Cuprum77/OpenTag/software/STM32WB_BT_TAG/STM32_WPAN/App/app_ble.c

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

/* Includes ------------------------------------------------------------------*/
#include "main.h"

#include "app_common.h"

#include "dbg_trace.h"
#include "ble.h"
#include "tl.h"
#include "app_ble.h"

#include "stm32_seq.h"
#include "shci.h"
#include "stm32_lpm.h"
#include "otp.h"

#include "custom_app.h"

/* USER CODE BEGIN Includes */
#include "stm32_lpm.h"
/* USER CODE END Includes */


/**
 * security parameters structure
 */
typedef struct _tSecurityParams
{
  /**
   * IO capability of the device
   */
  uint8_t ioCapability;

  /**
   * Authentication requirement of the device
   * Man In the Middle protection required?
   */
  uint8_t mitm_mode;

  /**
   * bonding mode of the device
   */
  uint8_t bonding_mode;

  /**
   * this variable indicates whether to use a fixed pin
   * during the pairing process or a passkey has to be
   * requested to the application during the pairing process
   * 0 implies use fixed pin and 1 implies request for passkey
   */
  uint8_t Use_Fixed_Pin;

  /**
   * minimum encryption key size requirement
   */
  uint8_t encryptionKeySizeMin;

  /**
   * maximum encryption key size requirement
   */
  uint8_t encryptionKeySizeMax;

  /**
   * fixed pin to be used in the pairing process if
   * Use_Fixed_Pin is set to 1
   */
  uint32_t Fixed_Pin;

  /**
   * this flag indicates whether the host has to initiate
   * the security, wait for pairing or does not have any security
   * requirements.
   * 0x00 : no security required
   * 0x01 : host should initiate security by sending the slave security
   *        request command
   * 0x02 : host need not send the clave security request but it
   * has to wait for paiirng to complete before doing any other
   * processing
   */
  uint8_t initiateSecurity;
  /* USER CODE BEGIN tSecurityParams*/

  /* USER CODE END tSecurityParams */
}tSecurityParams;

/**
 * global context
 * contains the variables common to all
 * services
 */
typedef struct _tBLEProfileGlobalContext
{
  /**
   * security requirements of the host
   */
  tSecurityParams bleSecurityParam;

  /**
   * gap service handle
   */
  uint16_t gapServiceHandle;

  /**
   * device name characteristic handle
   */
  uint16_t devNameCharHandle;

  /**
   * appearance characteristic handle
   */
  uint16_t appearanceCharHandle;

  /**
   * connection handle of the current active connection
   * When not in connection, the handle is set to 0xFFFF
   */
  uint16_t connectionHandle;

  /**
   * length of the UUID list to be used while advertising
   */
  uint8_t advtServUUIDlen;

  /**
   * the UUID list to be used while advertising
   */
  uint8_t advtServUUID[100];
  /* USER CODE BEGIN BleGlobalContext_t*/

  /* USER CODE END BleGlobalContext_t */
}BleGlobalContext_t;

typedef struct
{
  BleGlobalContext_t BleApplicationContext_legacy;
  APP_BLE_ConnStatus_t Device_Connection_Status;
  /* USER CODE BEGIN PTD_1*/

  /* USER CODE END PTD_1 */
}BleApplicationContext_t;

#define FAST_ADV_TIMEOUT               (30*1000*1000/CFG_TS_TICK_VAL) /**< 30s */
#define INITIAL_ADV_TIMEOUT            (60*1000*1000/CFG_TS_TICK_VAL) /**< 60s */

#define BD_ADDR_SIZE_LOCAL    6

/* USER CODE BEGIN PD */
/* Defines how long the tag will stay on and not go to sleep after a cold startup
 * This is useful to connect to a debugger or to check if the advertised payload is correct.
 */
#define COLD_START_ACTIVE_TIME_S 30

/*
* Turn on the LED when sending out advertising data, this is useful for debugging to see when the tag is advertising
* but should be disabled for normal use to save power. 
* (comment out to disable)
*/
#define ENABLE_ADV_LED_DEBUG

/* Defines the address where the airtag keys are put, this can be done with stm32cubeprogrammer, in the erasing and programming section,
 * you put in this address, select the option to NOT skip flash erase and program. The linker in this cubemx project is setup to not overwrite a 64k region after this address.
 */
#define KEY_ADDR_GOOGLE 0x08020000
#define KEY_ADDR_APPLE 0x08030000

#define GOOGLE_EID_LEN_BYTES 20
#define APPLE_KEY_LEN_BYTES 28

#define GOOGLE_NUMKEYS_FIELD_BYTES 2
#define APPLE_NUMKEYS_FIELD_BYTES 1

typedef enum adv_type {
  APPLE = 0,
  GOOGLE = 1
} adv_type_t;

// You can define the order and frequency of advertising here.
// Examples:
// adv_type_t adv_order[] = {APPLE, GOOGLE};          // alternate each cycle
// adv_type_t adv_order[] = {APPLE, APPLE, GOOGLE};   // advertise Apple twice as much as Google
// adv_type_t adv_order[] = {APPLE};                  // only advertise Apple
// adv_type_t adv_order[] = {GOOGLE};                 // only advertise Google
// Note that switching between the advertisement types takes a bit more time and thus energy
// So, it is better to repeat a key a few times before switching
adv_type_t adv_order[] = {APPLE, APPLE, APPLE, GOOGLE, GOOGLE, GOOGLE};

#define ADV_ORDER_LEN (sizeof(adv_order) / sizeof(adv_order[0]))

// Counted on startup and then used later to gate logic (so we can skip the paths that are never advertising)
int num_google = -1;
int num_apple = -1;
size_t adv_order_index = 0;

/* Define how often (long) a key will be reused after switching to the next one
 * The interval for one key is (DELAY_IN_S * REUSE_CYCLES => 10s * 360 cycles = changes key every 60 min)
 * Smaller number of cycles = key changes more often, but more keys needed.
 * You can calculate how much time it will take for all keys to be used up and it will roll around:
 * (DELAY_IN_S * REUSE_CYCLES * NUM_KEYS => 10s * 360 cycles * 32 keys = keys will wrap around every 32 hours)
 */
#define REUSE_CYCLES 360

/* A sleep cycle is 10 seconds of sleep, so 2 cycles is 20 seconds of sleep and so on.*/
#define SLEEP_CYCLES 1
/* USER CODE END PD */

PLACE_IN_SECTION("MB_MEM1") ALIGN(4) static TL_CmdPacket_t BleCmdBuffer;

static const uint8_t a_MBdAddr[BD_ADDR_SIZE_LOCAL] =
{
  (uint8_t)((CFG_ADV_BD_ADDRESS & 0x0000000000FF)),
  (uint8_t)((CFG_ADV_BD_ADDRESS & 0x00000000FF00) >> 8),
  (uint8_t)((CFG_ADV_BD_ADDRESS & 0x000000FF0000) >> 16),
  (uint8_t)((CFG_ADV_BD_ADDRESS & 0x0000FF000000) >> 24),
  (uint8_t)((CFG_ADV_BD_ADDRESS & 0x00FF00000000) >> 32),
  (uint8_t)((CFG_ADV_BD_ADDRESS & 0xFF0000000000) >> 40)
};

static uint8_t a_BdAddrUdn[BD_ADDR_SIZE_LOCAL];

/**
 *   Identity root key used to derive IRK and DHK(Legacy)
 */
static const uint8_t a_BLE_CfgIrValue[16] = CFG_BLE_IR;

/**
 * Encryption root key used to derive LTK(Legacy) and CSRK
 */
static const uint8_t a_BLE_CfgErValue[16] = CFG_BLE_ER;

/**
 * These are the two tags used to manage a power failure during OTA
 * The MagicKeywordAdress shall be mapped @0x140 from start of the binary image
 * The MagicKeywordvalue is checked in the ble_ota application
 */
PLACE_IN_SECTION("TAG_OTA_END") const uint32_t MagicKeywordValue = 0x94448A29 ;
PLACE_IN_SECTION("TAG_OTA_START") const uint32_t MagicKeywordAddress = (uint32_t)&MagicKeywordValue;

static BleApplicationContext_t BleApplicationContext;

Custom_App_ConnHandle_Not_evt_t HandleNotification;

#if (L2CAP_REQUEST_NEW_CONN_PARAM != 0)
#define SIZE_TAB_CONN_INT            2
float a_ConnInterval[SIZE_TAB_CONN_INT] = {50, 1000}; /* ms */
uint8_t index_con_int, mutex;
#endif /* L2CAP_REQUEST_NEW_CONN_PARAM != 0 */

/**
 * Advertising Data
 */
uint8_t a_AdvData[5] =
{
  4, AD_TYPE_MANUFACTURER_SPECIFIC_DATA, 0x4C, 0x00, 0xAA /* Does this even do anything? */,
};

/* USER CODE BEGIN PV */
const uint8_t apple_adv_data_template[31] = {
  0x1e,       /* Length (30) */                                   // 0            <- Static
  0xff,       /* Manufacturer Specific Data (type 0xff) */        // 1            <- Static
  0x4c, 0x00, /* Company ID (Apple) */                            // 2 3          <- Static
  0x12, 0x19, /* Offline Finding type and length */               // 4 5          <- Static
  0x00,       /* State */                                         // 6            <- Static
  0x00, 0x00, 0x00, 0x00, 0x00, 0x00, 0x00, 0x00,                 // 7 - 14    }
  0x00, 0x00, 0x00, 0x00, 0x00, 0x00, 0x00, 0x00,                 // 15 - 22   }  <- 22 bytes of public key
  0x00, 0x00, 0x00, 0x00, 0x00, 0x00,                             // 23 - 28   }
  0x00, /* First two bits */                                      // 29           <- 2 bits of public key
  0x00, /* Hint (0x00) */                                         // 30           <- Static
};

const uint8_t google_adv_data_template[31] = {
    0x02,   // Length                             // 0            <- Static
    0x01,   // Flags data type value              // 1            <- Static
    0x06,   // Flags data                         // 2            <- Static
    0x19,   // Length                             // 3            <- Static
    0x16,   // Service data data type value       // 4            <- Static
    0xAA,   // 16-bit service UUID                // 5            <- Static
    0xFE,   // 16-bit service UUID                // 6            <- Static
    0x41,   // FMDN frame type with unwanted      // 7            <- Static
            // tracking protection mode indication
    0x00, 0x00, 0x00, 0x00, 0x00,                 // 8 - 12   }
    0x00, 0x00, 0x00, 0x00, 0x00,                 // 13 - 17  }   <- 20-byte ephemeral identifier
    0x00, 0x00, 0x00, 0x00, 0x00,                 // 18 - 22  }
    0x00, 0x00, 0x00, 0x00, 0x00,                 // 23 - 27  }
    0x00, 0x00, 0x00, // Hashed flags             // 28 - 30
};

// our own advertising data, because cubemx has a limitation to a max length of 21 for some reason
uint8_t custom_a_AdvData[31] = { 0 };

// set our own variable for the MAC address
uint8_t custom_p_bd_addr[6] = {
  0xFF, 0xCC, 0xCC, 0xCC, 0xCC, 0xFF
};

static uint8_t public_key_apple[APPLE_KEY_LEN_BYTES] = { 0 };
static uint8_t public_key_google[GOOGLE_EID_LEN_BYTES] = { 0 };
static uint8_t google_mac_addr[6] = { 0 };
static bool google_mac_valid = false;

uint8_t key_index_apple = 0;
uint8_t old_key_index_apple = 0;
uint16_t key_count_apple = 0;
uint16_t key_cycle_apple = 0;

uint16_t key_index_google = 0;
uint16_t old_key_index_google = 0;
uint16_t key_count_google = 0;
uint16_t key_cycle_google = 0;

adv_type_t current_adv_type = APPLE;

/* USER CODE END PV */

static void BLE_UserEvtRx(void *p_Payload);
static void BLE_StatusNot(HCI_TL_CmdStatus_t Status);
static void Ble_Tl_Init(void);
static void Ble_Hci_Gap_Gatt_Init(void);
static const uint8_t* BleGetBdAddress(void);
static void Adv_Request(APP_BLE_ConnStatus_t NewStatus);
static void Adv_Cancel(void);
#if (L2CAP_REQUEST_NEW_CONN_PARAM != 0)
static void BLE_SVC_L2CAP_Conn_Update(uint16_t ConnectionHandle);
static void Connection_Interval_Update_Req(void);
#endif /* L2CAP_REQUEST_NEW_CONN_PARAM != 0 */

/* USER CODE BEGIN PFP */
void SystemClock_Config_ble(void);
RTC_HandleTypeDef hrtc_ble;
static void MX_RTC_Init_ble(void);
static void load_bytes_from_partition(uint8_t *dst, size_t size, uint32_t address);
void set_addr_from_key(uint8_t *addr, uint8_t *public_key, adv_type_t type);
void set_payload_from_key(uint8_t *payload, uint8_t *public_key, adv_type_t type);
adv_type_t get_adv_type_from_order(void);
void advance_adv_order(void);
/* USER CODE END PFP */

/* External variables --------------------------------------------------------*/

/* Functions Definition ------------------------------------------------------*/
void APP_BLE_Init(void)
{
  SHCI_CmdStatus_t status;
#if (RADIO_ACTIVITY_EVENT != 0)
  tBleStatus ret = BLE_STATUS_INVALID_PARAMS;
#endif /* RADIO_ACTIVITY_EVENT != 0 */
  /* USER CODE BEGIN APP_BLE_Init_1 */
  UTIL_SEQ_Init();

  num_apple = 0;
  num_google = 0;
  // Count the number of keys of each in the sequence
  for (size_t i = 0; i < ADV_ORDER_LEN; i++)
  {
    if (adv_order[i] == APPLE)
    {
      num_apple++;
    }
    else if (adv_order[i] == GOOGLE)
    {
      num_google++;
    }
  }

  current_adv_type = get_adv_type_from_order();
  
  uint8_t keyCountApple[APPLE_NUMKEYS_FIELD_BYTES];
  if (num_apple > 0)
  {
    load_bytes_from_partition(keyCountApple, sizeof(keyCountApple), KEY_ADDR_APPLE);
#if APPLE_NUMKEYS_FIELD_BYTES == 1
    key_count_apple = keyCountApple[0];
#elif APPLE_NUMKEYS_FIELD_BYTES == 2
    key_count_apple = keyCountApple[0] | (keyCountApple[1] << 8);
#endif
  }

  uint8_t keyCountGoogle[GOOGLE_NUMKEYS_FIELD_BYTES];
  if (num_google > 0)
  {
    load_bytes_from_partition(keyCountGoogle, sizeof(keyCountGoogle), KEY_ADDR_GOOGLE);
#if GOOGLE_NUMKEYS_FIELD_BYTES == 1
    key_count_google = keyCountGoogle[0];
#elif GOOGLE_NUMKEYS_FIELD_BYTES == 2
    key_count_google = keyCountGoogle[0] | (keyCountGoogle[1] << 8);
#endif
  }

  // choose a random key to start with
  if (num_apple > 0 && key_count_apple > 0)
  {
	  key_index_apple = HAL_GetTick() % key_count_apple;
  }
  if (num_google > 0 && key_count_google > 0)
  {
	  key_index_google = HAL_GetTick() % key_count_google;
  }

  if(key_count_apple == key_count_google){
	  key_index_google = key_index_apple;
  }

  old_key_index_apple = key_index_apple;
  old_key_index_google = key_index_google;
  key_cycle_apple = 0;
  key_cycle_google = 0;
  

  if (num_apple > 0)
  {
    uint32_t addressApple = APPLE_NUMKEYS_FIELD_BYTES + (key_index_apple * sizeof(public_key_apple)) + KEY_ADDR_APPLE;
    load_bytes_from_partition(public_key_apple, sizeof(public_key_apple), addressApple);
  }

  if (num_google > 0)
  {
    uint32_t addressGoogle = GOOGLE_NUMKEYS_FIELD_BYTES + (key_index_google * sizeof(public_key_google)) + KEY_ADDR_GOOGLE;
    load_bytes_from_partition(public_key_google, sizeof(public_key_google), addressGoogle);
    set_addr_from_key(google_mac_addr, public_key_google, GOOGLE);
    google_mac_valid = true;
  }

  // set the address and payload from the key
  if(current_adv_type == APPLE) {
    set_addr_from_key(custom_p_bd_addr, public_key_apple, current_adv_type);
    set_payload_from_key(custom_a_AdvData, public_key_apple, current_adv_type);
  } else {
    if (google_mac_valid)
    {
      memcpy(custom_p_bd_addr, google_mac_addr, sizeof(custom_p_bd_addr));
    }
    else
    {
      set_addr_from_key(google_mac_addr, public_key_google, GOOGLE);
      google_mac_valid = true;
      memcpy(custom_p_bd_addr, google_mac_addr, sizeof(custom_p_bd_addr));
    }
    set_payload_from_key(custom_a_AdvData, public_key_google, current_adv_type);
  }
  /* USER CODE END APP_BLE_Init_1 */
  SHCI_C2_Ble_Init_Cmd_Packet_t ble_init_cmd_packet =
  {
    {{0,0,0}},                          /**< Header unused */
    {0,                                 /** pBleBufferAddress not used */
     0,                                 /** BleBufferSize not used */
     CFG_BLE_NUM_GATT_ATTRIBUTES,
     CFG_BLE_NUM_GATT_SERVICES,
     CFG_BLE_ATT_VALUE_ARRAY_SIZE,
     CFG_BLE_NUM_LINK,
     CFG_BLE_DATA_LENGTH_EXTENSION,
     CFG_BLE_PREPARE_WRITE_LIST_SIZE,
     CFG_BLE_MBLOCK_COUNT,
     CFG_BLE_MAX_ATT_MTU,
     CFG_BLE_PERIPHERAL_SCA,
     CFG_BLE_CENTRAL_SCA,
     CFG_BLE_LS_SOURCE,
     CFG_BLE_MAX_CONN_EVENT_LENGTH,
     CFG_BLE_HSE_STARTUP_TIME,
     CFG_BLE_VITERBI_MODE,
     CFG_BLE_OPTIONS,
     0,
     CFG_BLE_MAX_COC_INITIATOR_NBR,
     CFG_BLE_MIN_TX_POWER,
     CFG_BLE_MAX_TX_POWER,
     CFG_BLE_RX_MODEL_CONFIG,
     CFG_BLE_MAX_ADV_SET_NBR,
     CFG_BLE_MAX_ADV_DATA_LEN,
     CFG_BLE_TX_PATH_COMPENS,
     CFG_BLE_RX_PATH_COMPENS,
     CFG_BLE_CORE_VERSION,
     CFG_BLE_OPTIONS_EXT
    }
  };

  /**
   * Initialize Ble Transport Layer
   */
  Ble_Tl_Init();

  /**
   * Do not allow standby in the application
   */
  UTIL_LPM_SetOffMode(1 << CFG_LPM_APP_BLE, UTIL_LPM_DISABLE);

  /**
   * Register the hci transport layer to handle BLE User Asynchronous Events
   */
  UTIL_SEQ_RegTask(1<<CFG_TASK_HCI_ASYNCH_EVT_ID, UTIL_SEQ_RFU, hci_user_evt_proc);

  /**
   * Starts the BLE Stack on CPU2
   */
  status = SHCI_C2_BLE_Init(&ble_init_cmd_packet);
  if (status != SHCI_Success)
  {
    APP_DBG_MSG("  Fail   : SHCI_C2_BLE_Init command, result: 0x%02x\n\r", status);
    /* if you are here, maybe CPU2 doesn't contain STM32WB_Copro_Wireless_Binaries, see Release_Notes.html */
    Error_Handler();
  }
  else
  {
    APP_DBG_MSG("  Success: SHCI_C2_BLE_Init command\n\r");
  }

  /**
   * Initialization of HCI & GATT & GAP layer
   */
  Ble_Hci_Gap_Gatt_Init();

  /**
   * Initialization of the BLE Services
   */
  SVCCTL_Init();

  /**
   * Initialization of the BLE App Context
   */
  BleApplicationContext.Device_Connection_Status = APP_BLE_IDLE;
  BleApplicationContext.BleApplicationContext_legacy.connectionHandle = 0xFFFF;

  /**
   * From here, all initialization are BLE application specific
   */

  UTIL_SEQ_RegTask(1<<CFG_TASK_ADV_CANCEL_ID, UTIL_SEQ_RFU, Adv_Cancel);

  /**
   * Initialization of ADV - Ad Manufacturer Element - Support OTA Bit Mask
   */
#if (RADIO_ACTIVITY_EVENT != 0)
  ret = aci_hal_set_radio_activity_mask(0x0006);
  if (ret != BLE_STATUS_SUCCESS)
  {
    APP_DBG_MSG("  Fail   : aci_hal_set_radio_activity_mask command, result: 0x%x \n\r", ret);
  }
  else
  {
    APP_DBG_MSG("  Success: aci_hal_set_radio_activity_mask command\n\r");
  }
#endif /* RADIO_ACTIVITY_EVENT != 0 */

#if (L2CAP_REQUEST_NEW_CONN_PARAM != 0)
  index_con_int = 0;
  mutex = 1;
#endif /* L2CAP_REQUEST_NEW_CONN_PARAM != 0 */

  /**
   * Initialize Custom Template Application
   */
  Custom_APP_Init();

  /**
   * Make device discoverable
   */
  BleApplicationContext.BleApplicationContext_legacy.advtServUUID[0] = NULL;
  BleApplicationContext.BleApplicationContext_legacy.advtServUUIDlen = 0;

  /**
   * Start to Advertise to be connected by a Client
   */
  Adv_Request(APP_BLE_FAST_ADV);

  /* USER CODE BEGIN APP_BLE_Init_2 */
  // register our task to send out advertising data
  UTIL_SEQ_RegTask((1 << 9), UTIL_SEQ_RFU, Send_Out_Adv);
  UTIL_SEQ_SetTask((1 << 9), CFG_SCH_PRIO_0);
  MX_RTC_Init_ble();
  /* USER CODE END APP_BLE_Init_2 */

  return;
}

SVCCTL_UserEvtFlowStatus_t SVCCTL_App_Notification(void *p_Pckt)
{
  hci_event_pckt    *p_event_pckt;
  evt_le_meta_event *p_meta_evt;
  evt_blecore_aci   *p_blecore_evt;
  tBleStatus        ret = BLE_STATUS_INVALID_PARAMS;
  hci_le_connection_complete_event_rp0        *p_connection_complete_event;
  hci_disconnection_complete_event_rp0        *p_disconnection_complete_event;
#if (CFG_DEBUG_APP_TRACE != 0)
  hci_le_connection_update_complete_event_rp0 *p_connection_update_complete_event;
#endif /* CFG_DEBUG_APP_TRACE != 0 */

  /* PAIRING */
  aci_gap_pairing_complete_event_rp0          *p_pairing_complete;
  /* PAIRING */

  p_event_pckt = (hci_event_pckt*) ((hci_uart_pckt *) p_Pckt)->data;

  switch (p_event_pckt->evt)
  {
    case HCI_DISCONNECTION_COMPLETE_EVT_CODE:
    {
      p_disconnection_complete_event = (hci_disconnection_complete_event_rp0 *) p_event_pckt->data;

      if (p_disconnection_complete_event->Connection_Handle == BleApplicationContext.BleApplicationContext_legacy.connectionHandle)
      {
        BleApplicationContext.BleApplicationContext_legacy.connectionHandle = 0;
        BleApplicationContext.Device_Connection_Status = APP_BLE_IDLE;
        APP_DBG_MSG(">>== HCI_DISCONNECTION_COMPLETE_EVT_CODE\n");
        APP_DBG_MSG("     - Connection Handle:   0x%x\n     - Reason:    0x%x\n\r",
                    p_disconnection_complete_event->Connection_Handle,
                    p_disconnection_complete_event->Reason);

      }

      /* restart advertising */
      Adv_Request(APP_BLE_FAST_ADV);

      /**
       * SPECIFIC to Custom Template APP
       */
      HandleNotification.Custom_Evt_Opcode = CUSTOM_DISCON_HANDLE_EVT;
      HandleNotification.ConnectionHandle = BleApplicationContext.BleApplicationContext_legacy.connectionHandle;
      Custom_APP_Notification(&HandleNotification);
      break; /* HCI_DISCONNECTION_COMPLETE_EVT_CODE */
    }

    case HCI_LE_META_EVT_CODE:
    {
      p_meta_evt = (evt_le_meta_event*) p_event_pckt->data;
      switch (p_meta_evt->subevent)
      {
        case HCI_LE_CONNECTION_UPDATE_COMPLETE_SUBEVT_CODE:
#if (CFG_DEBUG_APP_TRACE != 0)
          p_connection_update_complete_event = (hci_le_connection_update_complete_event_rp0 *) p_meta_evt->data;
          APP_DBG_MSG(">>== HCI_LE_CONNECTION_UPDATE_COMPLETE_SUBEVT_CODE\n");
          APP_DBG_MSG("     - Connection Interval:   %.2f ms\n     - Connection latency:    %d\n     - Supervision Timeout: %d ms\n\r",
                       p_connection_update_complete_event->Conn_Interval*1.25,
                       p_connection_update_complete_event->Conn_Latency,
                       p_connection_update_complete_event->Supervision_Timeout*10);
#endif /* CFG_DEBUG_APP_TRACE != 0 */

          break;

        case HCI_LE_CONNECTION_COMPLETE_SUBEVT_CODE:
        {
          p_connection_complete_event = (hci_le_connection_complete_event_rp0 *) p_meta_evt->data;
          /**
           * The connection is done, there is no need anymore to schedule the LP ADV
           */

          APP_DBG_MSG(">>== HCI_LE_CONNECTION_COMPLETE_SUBEVT_CODE - Connection handle: 0x%x\n", p_connection_complete_event->Connection_Handle);
          APP_DBG_MSG("     - Connection established with Central: @:%02x:%02x:%02x:%02x:%02x:%02x\n",
                      p_connection_complete_event->Peer_Address[5],
                      p_connection_complete_event->Peer_Address[4],
                      p_connection_complete_event->Peer_Address[3],
                      p_connection_complete_event->Peer_Address[2],
                      p_connection_complete_event->Peer_Address[1],
                      p_connection_complete_event->Peer_Address[0]);
          APP_DBG_MSG("     - Connection Interval:   %.2f ms\n     - Connection latency:    %d\n     - Supervision Timeout: %d ms\n\r",
                      p_connection_complete_event->Conn_Interval*1.25,
                      p_connection_complete_event->Conn_Latency,
                      p_connection_complete_event->Supervision_Timeout*10
                     );

          if (BleApplicationContext.Device_Connection_Status == APP_BLE_LP_CONNECTING)
          {
            /* Connection as client */
            BleApplicationContext.Device_Connection_Status = APP_BLE_CONNECTED_CLIENT;
          }
          else
          {
            /* Connection as server */
            BleApplicationContext.Device_Connection_Status = APP_BLE_CONNECTED_SERVER;
          }
          BleApplicationContext.BleApplicationContext_legacy.connectionHandle = p_connection_complete_event->Connection_Handle;
          /**
           * SPECIFIC to Custom Template APP
           */
          HandleNotification.Custom_Evt_Opcode = CUSTOM_CONN_HANDLE_EVT;
          HandleNotification.ConnectionHandle = BleApplicationContext.BleApplicationContext_legacy.connectionHandle;
          Custom_APP_Notification(&HandleNotification);
          break; /* HCI_LE_CONNECTION_COMPLETE_SUBEVT_CODE */
        }

        default:
          break;
      }

      break; /* HCI_LE_META_EVT_CODE */
    }

    case HCI_VENDOR_SPECIFIC_DEBUG_EVT_CODE:
      p_blecore_evt = (evt_blecore_aci*) p_event_pckt->data;
      switch (p_blecore_evt->ecode)
      {
        /**
         * SPECIFIC to Custom Template APP
         */
        case ACI_L2CAP_CONNECTION_UPDATE_RESP_VSEVT_CODE:
#if (L2CAP_REQUEST_NEW_CONN_PARAM != 0)
          mutex = 1;
#endif /* L2CAP_REQUEST_NEW_CONN_PARAM != 0 */
          /* USER CODE BEGIN EVT_BLUE_L2CAP_CONNECTION_UPDATE_RESP */

          /* USER CODE END EVT_BLUE_L2CAP_CONNECTION_UPDATE_RESP */
          break;

        case ACI_GAP_PROC_COMPLETE_VSEVT_CODE:
          APP_DBG_MSG(">>== ACI_GAP_PROC_COMPLETE_VSEVT_CODE \r");
          /* USER CODE BEGIN EVT_BLUE_GAP_PROCEDURE_COMPLETE */

          /* USER CODE END EVT_BLUE_GAP_PROCEDURE_COMPLETE */
          break; /* ACI_GAP_PROC_COMPLETE_VSEVT_CODE */

#if (RADIO_ACTIVITY_EVENT != 0)
        case ACI_HAL_END_OF_RADIO_ACTIVITY_VSEVT_CODE:
          /* USER CODE BEGIN RADIO_ACTIVITY_EVENT*/
          // HAL_GPIO_TogglePin(LED_PIN_GPIO_Port, LED_PIN_Pin);
          /* USER CODE END RADIO_ACTIVITY_EVENT*/
          break; /* ACI_HAL_END_OF_RADIO_ACTIVITY_VSEVT_CODE */
#endif /* RADIO_ACTIVITY_EVENT != 0 */

        /* PAIRING */
        case (ACI_GAP_KEYPRESS_NOTIFICATION_VSEVT_CODE):
          APP_DBG_MSG(">>== ACI_GAP_KEYPRESS_NOTIFICATION_VSEVT_CODE\n");
          /* USER CODE BEGIN ACI_GAP_KEYPRESS_NOTIFICATION_VSEVT_CODE*/

          /* USER CODE END ACI_GAP_KEYPRESS_NOTIFICATION_VSEVT_CODE*/
          break;

        case ACI_GAP_PASS_KEY_REQ_VSEVT_CODE:
          APP_DBG_MSG(">>== ACI_GAP_PASS_KEY_REQ_VSEVT_CODE \n");

          ret = aci_gap_pass_key_resp(BleApplicationContext.BleApplicationContext_legacy.connectionHandle, CFG_FIXED_PIN);
          if (ret != BLE_STATUS_SUCCESS)
          {
            APP_DBG_MSG("==>> aci_gap_pass_key_resp : Fail, reason: 0x%x\n", ret);
          }
          else
          {
            APP_DBG_MSG("==>> aci_gap_pass_key_resp : Success \n");
          }
          /* USER CODE BEGIN ACI_GAP_PASS_KEY_REQ_VSEVT_CODE*/

          /* USER CODE END ACI_GAP_PASS_KEY_REQ_VSEVT_CODE*/
          break;

        case ACI_GAP_NUMERIC_COMPARISON_VALUE_VSEVT_CODE:
          APP_DBG_MSG(">>== ACI_GAP_NUMERIC_COMPARISON_VALUE_VSEVT_CODE\n");
          APP_DBG_MSG("     - numeric_value = %ld\n",
                      ((aci_gap_numeric_comparison_value_event_rp0 *)(p_blecore_evt->data))->Numeric_Value);
          APP_DBG_MSG("     - Hex_value = %lx\n",
                      ((aci_gap_numeric_comparison_value_event_rp0 *)(p_blecore_evt->data))->Numeric_Value);
          ret = aci_gap_numeric_comparison_value_confirm_yesno(BleApplicationContext.BleApplicationContext_legacy.connectionHandle, YES);
          if (ret != BLE_STATUS_SUCCESS)
          {
            APP_DBG_MSG("==>> aci_gap_numeric_comparison_value_confirm_yesno-->YES : Fail, reason: 0x%x\n", ret);
          }
          else
          {
            APP_DBG_MSG("==>> aci_gap_numeric_comparison_value_confirm_yesno-->YES : Success \n");
          }
          /* USER CODE BEGIN ACI_GAP_NUMERIC_COMPARISON_VALUE_VSEVT_CODE*/

          /* USER CODE END ACI_GAP_NUMERIC_COMPARISON_VALUE_VSEVT_CODE*/
          break;

        case ACI_GAP_PAIRING_COMPLETE_VSEVT_CODE:
          p_pairing_complete = (aci_gap_pairing_complete_event_rp0*)p_blecore_evt->data;

          APP_DBG_MSG(">>== ACI_GAP_PAIRING_COMPLETE_VSEVT_CODE\n");
          if (p_pairing_complete->Status != 0)
          {
            APP_DBG_MSG("     - Pairing KO \n     - Status: 0x%x\n     - Reason: 0x%x\n", p_pairing_complete->Status, p_pairing_complete->Reason);
          }
          else
          {
            APP_DBG_MSG("     - Pairing Success\n");
          }
          APP_DBG_MSG("\n");

          /* USER CODE BEGIN ACI_GAP_PAIRING_COMPLETE_VSEVT_CODE*/

          /* USER CODE END ACI_GAP_PAIRING_COMPLETE_VSEVT_CODE*/
          break;
        /* PAIRING */
        case ACI_GATT_INDICATION_VSEVT_CODE:
        {
          APP_DBG_MSG(">>== ACI_GATT_INDICATION_VSEVT_CODE \r");
          aci_gatt_confirm_indication(BleApplicationContext.BleApplicationContext_legacy.connectionHandle);
        }
        break;

      }
      break; /* HCI_VENDOR_SPECIFIC_DEBUG_EVT_CODE */

    default:
      /* USER CODE BEGIN ECODE_DEFAULT*/

      /* USER CODE END ECODE_DEFAULT*/
      break;
  }

  return (SVCCTL_UserEvtFlowEnable);
}

APP_BLE_ConnStatus_t APP_BLE_Get_Server_Connection_Status(void)
{
  return BleApplicationContext.Device_Connection_Status;
}

/* USER CODE BEGIN FD*/
void perform_advertising_cycle(adv_type_t type, bool rotate){
  static uint16_t adv_delay_len_ms = 18;
  static uint16_t adv_settings_delay_len_ms = 5;
  static uint16_t stop_adv_delay_len_ms = 1;
  static adv_type_t old_adv_type = 0xFF; // invalid value to force update on first run
  tBleStatus ret;
  if(type == APPLE){
    
    // Get the key as needed
    if(old_key_index_apple != key_index_apple){
      // key has changed, update the address and payload
      uint32_t address = APPLE_NUMKEYS_FIELD_BYTES + (key_index_apple * sizeof(public_key_apple)) + KEY_ADDR_APPLE;
      load_bytes_from_partition(public_key_apple, sizeof(public_key_apple), address);

      set_addr_from_key(custom_p_bd_addr, public_key_apple, APPLE);
      set_payload_from_key(custom_a_AdvData, public_key_apple, APPLE);

      // TODO check if this works
      // Ble_Hci_Gap_Gatt_Init();

      old_key_index_apple = key_index_apple;
    }
    
    if(old_adv_type != type){
      // adv type has changed, update the address and payload
      set_addr_from_key(custom_p_bd_addr, public_key_apple, APPLE);
      set_payload_from_key(custom_a_AdvData, public_key_apple, APPLE);
      ret = aci_hal_write_config_data(CONFIG_DATA_PUBADDR_OFFSET, CONFIG_DATA_PUBADDR_LEN, (uint8_t*)custom_p_bd_addr);
      if (ret != BLE_STATUS_SUCCESS)
      {
        APP_DBG_MSG("==>> Failed to update Apple advertising address, result: 0x%x\n", ret);
      }
      HAL_Delay(adv_settings_delay_len_ms);
      old_adv_type = type;
    }

    // start advertising
    Adv_Request(APP_BLE_FAST_ADV);
    // wait for a few ms for the 2nd core to start advertising
    HAL_Delay(adv_delay_len_ms);
    // stop advertising
    Adv_Cancel();
    // wait for 1ms for the 2nd core to stop advertising
    HAL_Delay(stop_adv_delay_len_ms);

    // increment key index for next time
    if ((key_cycle_apple >= REUSE_CYCLES) && rotate){
      key_index_apple = (key_index_apple + 1) % key_count_apple; // Back to zero if out of range
      key_cycle_apple = 0;
    }else{
      key_cycle_apple++;
    }

  }else if(type == GOOGLE){
    // Get the key as needed
    if(old_key_index_google != key_index_google){
      // key has changed, update the address and payload
      uint32_t address = GOOGLE_NUMKEYS_FIELD_BYTES + (key_index_google * sizeof(public_key_google)) + KEY_ADDR_GOOGLE;
      load_bytes_from_partition(public_key_google, sizeof(public_key_google), address);

      set_addr_from_key(google_mac_addr, public_key_google, GOOGLE);
      google_mac_valid = true;
      memcpy(custom_p_bd_addr, google_mac_addr, sizeof(custom_p_bd_addr));
      set_payload_from_key(custom_a_AdvData, public_key_google, GOOGLE);

      old_key_index_google = key_index_google;
    }

    if(old_adv_type != type){
      // adv type has changed, update the address and payload
      if (!google_mac_valid)
      {
        set_addr_from_key(google_mac_addr, public_key_google, GOOGLE);
        google_mac_valid = true;
      }
      memcpy(custom_p_bd_addr, google_mac_addr, sizeof(custom_p_bd_addr));
      set_payload_from_key(custom_a_AdvData, public_key_google, GOOGLE);
      ret = aci_hal_write_config_data(CONFIG_DATA_PUBADDR_OFFSET, CONFIG_DATA_PUBADDR_LEN, (uint8_t*)custom_p_bd_addr);
      if (ret != BLE_STATUS_SUCCESS)
      {
        APP_DBG_MSG("==>> Failed to update Google advertising address, result: 0x%x\n", ret);
      }
      HAL_Delay(adv_settings_delay_len_ms);
      old_adv_type = type;
    }

    // start advertising
    Adv_Request(APP_BLE_FAST_ADV);

    // wait for a few ms for the 2nd core to start advertising
    HAL_Delay(adv_delay_len_ms);

    // stop advertising
    Adv_Cancel();

    // wait for 1ms for the 2nd core to stop advertising
    HAL_Delay(stop_adv_delay_len_ms);

    // increment key index for next time
    if ((key_cycle_google >= REUSE_CYCLES) && rotate){
      key_index_google = (key_index_google + 1) % key_count_google; // Back to zero if out of range
      key_cycle_google = 0;
    }else{
      key_cycle_google++;
    }

  }
}

void Send_Out_Adv(void){

  #ifdef ENABLE_ADV_LED_DEBUG
    // turn on LED
    HAL_GPIO_WritePin(LED_PIN_GPIO_Port, LED_PIN_Pin, GPIO_PIN_SET);
  #endif
  
  if(cold_start_flag){
	  // keep the tag awake for the cold-start window
	  for(int i = 0; i < COLD_START_ACTIVE_TIME_S; i++){
		  HAL_GPIO_WritePin(LED_PIN_GPIO_Port, LED_PIN_Pin, GPIO_PIN_SET);
		  HAL_Delay(100);
      // Advertise both, for debugging purposes
      {
        current_adv_type = get_adv_type_from_order();
        perform_advertising_cycle(current_adv_type, false);
        advance_adv_order();
      }
		  HAL_GPIO_WritePin(LED_PIN_GPIO_Port, LED_PIN_Pin, GPIO_PIN_RESET);
		  HAL_Delay(900);
	  }

	  // blink one last time for a second to indicate that we are going to sleep
	  HAL_GPIO_WritePin(LED_PIN_GPIO_Port, LED_PIN_Pin, GPIO_PIN_SET);
	  HAL_Delay(1000);
	  HAL_GPIO_WritePin(LED_PIN_GPIO_Port, LED_PIN_Pin, GPIO_PIN_RESET);
	  cold_start_flag = false;
  }

  current_adv_type = get_adv_type_from_order();
  perform_advertising_cycle(current_adv_type, true);
  advance_adv_order();

  #ifdef ENABLE_ADV_LED_DEBUG
    // turn off LED
    HAL_GPIO_WritePin(LED_PIN_GPIO_Port, LED_PIN_Pin, GPIO_PIN_RESET);
  #endif

  // go back into deep sleep
  for(int i = 0; i < SLEEP_CYCLES; i++){
    //////// DEEP SLEEP START (~10seconds)
    HAL_SuspendTick();
    HAL_RTCEx_SetWakeUpTimer_IT(&hrtc_ble, 0x5554, RTC_WAKEUPCLOCK_RTCCLK_DIV16);
    /* Enter STOP 2 mode */
    HAL_PWREx_EnterSTOP2Mode(PWR_STOPENTRY_WFI);
    HAL_RTCEx_DeactivateWakeUpTimer(&hrtc_ble);
    SystemClock_Config_ble();
    HAL_ResumeTick();
    //////// DEEP SLEEP END  
  }
  
  UTIL_SEQ_SetTask((1 << 9), CFG_SCH_PRIO_0);
}

void set_payload_from_key(uint8_t *payload, uint8_t *public_key, adv_type_t type)
{
  if(type == APPLE){
    // Copy template into payload
    memcpy(payload, apple_adv_data_template, sizeof(apple_adv_data_template));

    // copy the key into the payload
    // last 22 bytes
    memcpy(&payload[7], &public_key[6], 22);
    // append two bits of public key
    payload[29] = public_key[0] >> 6;
  }else if(type == GOOGLE){
    // Copy template into payload
    memcpy(payload, google_adv_data_template, sizeof(google_adv_data_template));
    // copy 20-byte public key into payload
    memcpy(&payload[8], public_key, GOOGLE_EID_LEN_BYTES);
  }
}

void set_addr_from_key(uint8_t *addr, uint8_t *public_key, adv_type_t type)
{
  if(type == APPLE){
    addr[5] = public_key[0] | 0b11000000;
    addr[4] = public_key[1];
    addr[3] = public_key[2];
    addr[2] = public_key[3];
    addr[1] = public_key[4];
    addr[0] = public_key[5];
  }else if(type == GOOGLE){
    for (int i = 0; i < 6; i++) {
      uint8_t rng_byte = HAL_GetTick() % 256; // not cryptographically secure, but it's mixed with the key so it's fine
      addr[i] = public_key[i] ^ rng_byte; // XOR with a byte from the key to add some variability, since Google allows us to set the MAC to be random
    }
    // static random bits per: https://www.bluetooth.com/wp-content/uploads/Files/Specification/HTML/Core-54/out/en/low-energy-controller/link-layer-specification.html
    addr[5] |= 0b11000000; // set the two most significant bits to 1 to indicate that this is a static random address
  }
}

adv_type_t get_adv_type_from_order(void)
{
  return adv_order[adv_order_index];
}

void advance_adv_order(void)
{
  adv_order_index = (adv_order_index + 1) % ADV_ORDER_LEN;
}

static void load_bytes_from_partition(uint8_t *dst, size_t size, uint32_t address) {
  size_t i = 0;
  while (i * sizeof(uint32_t) < size) {  // Ensures loop runs even if size < 4
    uint32_t value = *(volatile uint32_t*)(address + i * sizeof(uint32_t));
    for (size_t j = 0; j < sizeof(uint32_t); j++) {
      size_t idx = i * sizeof(uint32_t) + j;
      if (idx >= size) {  // Prevents overflow
        return;
      }
      dst[idx] = (value >> (j * 8)) & 0xFF;
    }
    i++;
  }
}

void SystemClock_Config_ble(void)
{
  RCC_OscInitTypeDef RCC_OscInitStruct = {0};
  RCC_ClkInitTypeDef RCC_ClkInitStruct = {0};

  /** Configure LSE Drive Capability
  */
  HAL_PWR_EnableBkUpAccess();
  __HAL_RCC_LSEDRIVE_CONFIG(RCC_LSEDRIVE_MEDIUMHIGH);

  /** Initializes the RCC Oscillators according to the specified parameters
  * in the RCC_OscInitTypeDef structure.
  */
  RCC_OscInitStruct.OscillatorType = RCC_OSCILLATORTYPE_HSI|RCC_OSCILLATORTYPE_HSE
                              |RCC_OSCILLATORTYPE_LSE|RCC_OSCILLATORTYPE_MSI;
  RCC_OscInitStruct.HSEState = RCC_HSE_ON;
  RCC_OscInitStruct.LSEState = RCC_LSE_ON;
  RCC_OscInitStruct.HSIState = RCC_HSI_ON;
  RCC_OscInitStruct.MSIState = RCC_MSI_ON;
  RCC_OscInitStruct.HSICalibrationValue = RCC_HSICALIBRATION_DEFAULT;
  RCC_OscInitStruct.MSICalibrationValue = RCC_MSICALIBRATION_DEFAULT;
  RCC_OscInitStruct.MSIClockRange = RCC_MSIRANGE_10;
  RCC_OscInitStruct.PLL.PLLState = RCC_PLL_NONE;
  if (HAL_RCC_OscConfig(&RCC_OscInitStruct) != HAL_OK)
  {
    Error_Handler();
  }

  /** Configure the SYSCLKSource, HCLK, PCLK1 and PCLK2 clocks dividers
  */
  RCC_ClkInitStruct.ClockType = RCC_CLOCKTYPE_HCLK4|RCC_CLOCKTYPE_HCLK2
                              |RCC_CLOCKTYPE_HCLK|RCC_CLOCKTYPE_SYSCLK
                              |RCC_CLOCKTYPE_PCLK1|RCC_CLOCKTYPE_PCLK2;
  RCC_ClkInitStruct.SYSCLKSource = RCC_SYSCLKSOURCE_MSI;
  RCC_ClkInitStruct.AHBCLKDivider = RCC_SYSCLK_DIV1;
  RCC_ClkInitStruct.APB1CLKDivider = RCC_HCLK_DIV1;
  RCC_ClkInitStruct.APB2CLKDivider = RCC_HCLK_DIV1;
  RCC_ClkInitStruct.AHBCLK2Divider = RCC_SYSCLK_DIV1;
  RCC_ClkInitStruct.AHBCLK4Divider = RCC_SYSCLK_DIV1;

  if (HAL_RCC_ClockConfig(&RCC_ClkInitStruct, FLASH_LATENCY_1) != HAL_OK)
  {
    Error_Handler();
  }
}

static void MX_RTC_Init_ble(void)
{

  /** Initialize RTC Only
  */
  hrtc_ble.Instance = RTC;
  hrtc_ble.Init.HourFormat = RTC_HOURFORMAT_24;
  hrtc_ble.Init.AsynchPrediv = CFG_RTC_ASYNCH_PRESCALER;
  hrtc_ble.Init.SynchPrediv = CFG_RTC_SYNCH_PRESCALER;
  hrtc_ble.Init.OutPut = RTC_OUTPUT_DISABLE;
  hrtc_ble.Init.OutPutPolarity = RTC_OUTPUT_POLARITY_HIGH;
  hrtc_ble.Init.OutPutType = RTC_OUTPUT_TYPE_OPENDRAIN;
  hrtc_ble.Init.OutPutRemap = RTC_OUTPUT_REMAP_NONE;
  if (HAL_RTC_Init(&hrtc_ble) != HAL_OK)
  {
    Error_Handler();
  }

  /** Enable the WakeUp
  */
  if (HAL_RTCEx_SetWakeUpTimer_IT(&hrtc_ble, 0x500b, RTC_WAKEUPCLOCK_RTCCLK_DIV16) != HAL_OK)
  {
    Error_Handler();
  }
}

/* USER CODE END FD*/

/*************************************************************
 *
 * LOCAL FUNCTIONS
 *
 *************************************************************/
static void Ble_Tl_Init(void)
{
  HCI_TL_HciInitConf_t Hci_Tl_Init_Conf;

  Hci_Tl_Init_Conf.p_cmdbuffer = (uint8_t*)&BleCmdBuffer;
  Hci_Tl_Init_Conf.StatusNotCallBack = BLE_StatusNot;
  hci_init(BLE_UserEvtRx, (void*) &Hci_Tl_Init_Conf);

  return;
}

static void Ble_Hci_Gap_Gatt_Init(void)
{
  uint8_t role;
  uint16_t gap_service_handle, gap_dev_name_char_handle, gap_appearance_char_handle;
  const uint8_t *p_bd_addr;
  uint16_t a_appearance[1] = {BLE_CFG_GAP_APPEARANCE};
  tBleStatus ret = BLE_STATUS_INVALID_PARAMS;
  /* USER CODE BEGIN Ble_Hci_Gap_Gatt_Init*/

  /* USER CODE END Ble_Hci_Gap_Gatt_Init*/

  APP_DBG_MSG("==>> Start Ble_Hci_Gap_Gatt_Init function\n");

  /**
   * Initialize HCI layer
   */
  /*HCI Reset to synchronise BLE Stack*/
  ret = hci_reset();
  if (ret != BLE_STATUS_SUCCESS)
  {
    APP_DBG_MSG("  Fail   : hci_reset command, result: 0x%x \n", ret);
  }
  else
  {
    APP_DBG_MSG("  Success: hci_reset command\n");
  }

  /**
   * Write the BD Address
   */
  p_bd_addr = BleGetBdAddress();
  ret = aci_hal_write_config_data(CONFIG_DATA_PUBADDR_OFFSET, CONFIG_DATA_PUBADDR_LEN, (uint8_t*) p_bd_addr);
  if (ret != BLE_STATUS_SUCCESS)
  {
    APP_DBG_MSG("  Fail   : aci_hal_write_config_data command - CONFIG_DATA_PUBADDR_OFFSET, result: 0x%x \n", ret);
  }
  else
  {
    APP_DBG_MSG("  Success: aci_hal_write_config_data command - CONFIG_DATA_PUBADDR_OFFSET\n");
    APP_DBG_MSG("  Public Bluetooth Address: %02x:%02x:%02x:%02x:%02x:%02x\n",p_bd_addr[5],p_bd_addr[4],p_bd_addr[3],p_bd_addr[2],p_bd_addr[1],p_bd_addr[0]);
  }

  /**
   * Static random Address
   * The two upper bits shall be set to 1
   * The lowest 32bits is read from the UDN to differentiate between devices
   * The RNG may be used to provide a random number on each power on
   */
#if (CFG_BLE_ADDRESS_TYPE != GAP_PUBLIC_ADDR)

  ret = aci_hal_write_config_data(CONFIG_DATA_RANDOM_ADDRESS_OFFSET, CONFIG_DATA_RANDOM_ADDRESS_LEN, (uint8_t*)a_srd_bd_addr);
  if (ret != BLE_STATUS_SUCCESS)
  {
    APP_DBG_MSG("  Fail   : aci_hal_write_config_data command - CONFIG_DATA_RANDOM_ADDRESS_OFFSET, result: 0x%x \n", ret);
  }
  else
  {
    APP_DBG_MSG("  Success: aci_hal_write_config_data command - CONFIG_DATA_RANDOM_ADDRESS_OFFSET\n");
    APP_DBG_MSG("  Random Bluetooth Address: %02x:%02x:%02x:%02x:%02x:%02x\n", (uint8_t)(a_srd_bd_addr[1] >> 8),
                                                                               (uint8_t)(a_srd_bd_addr[1]),
                                                                               (uint8_t)(a_srd_bd_addr[0] >> 24),
                                                                               (uint8_t)(a_srd_bd_addr[0] >> 16),
                                                                               (uint8_t)(a_srd_bd_addr[0] >> 8),
                                                                               (uint8_t)(a_srd_bd_addr[0]));
  }
#endif /* CFG_BLE_ADDRESS_TYPE != GAP_PUBLIC_ADDR */

  /**
   * Write Identity root key used to derive IRK and DHK(Legacy)
   */
  ret = aci_hal_write_config_data(CONFIG_DATA_IR_OFFSET, CONFIG_DATA_IR_LEN, (uint8_t*)a_BLE_CfgIrValue);
  if (ret != BLE_STATUS_SUCCESS)
  {
    APP_DBG_MSG("  Fail   : aci_hal_write_config_data command - CONFIG_DATA_IR_OFFSET, result: 0x%x \n", ret);
  }
  else
  {
    APP_DBG_MSG("  Success: aci_hal_write_config_data command - CONFIG_DATA_IR_OFFSET\n");
  }

  /**
   * Write Encryption root key used to derive LTK and CSRK
   */
  ret = aci_hal_write_config_data(CONFIG_DATA_ER_OFFSET, CONFIG_DATA_ER_LEN, (uint8_t*)a_BLE_CfgErValue);
  if (ret != BLE_STATUS_SUCCESS)
  {
    APP_DBG_MSG("  Fail   : aci_hal_write_config_data command - CONFIG_DATA_ER_OFFSET, result: 0x%x \n", ret);
  }
  else
  {
    APP_DBG_MSG("  Success: aci_hal_write_config_data command - CONFIG_DATA_ER_OFFSET\n");
  }

  /**
   * Set TX Power.
   */
  ret = aci_hal_set_tx_power_level(1, CFG_TX_POWER);
  if (ret != BLE_STATUS_SUCCESS)
  {
    APP_DBG_MSG("  Fail   : aci_hal_set_tx_power_level command, result: 0x%x \n", ret);
  }
  else
  {
    APP_DBG_MSG("  Success: aci_hal_set_tx_power_level command\n");
  }

  /**
   * Initialize GATT interface
   */
  ret = aci_gatt_init();
  if (ret != BLE_STATUS_SUCCESS)
  {
    APP_DBG_MSG("  Fail   : aci_gatt_init command, result: 0x%x \n", ret);
  }
  else
  {
    APP_DBG_MSG("  Success: aci_gatt_init command\n");
  }

  /**
   * Initialize GAP interface
   */
  role = 0;

#if (BLE_CFG_PERIPHERAL == 1)
  role |= GAP_PERIPHERAL_ROLE;
#endif /* BLE_CFG_PERIPHERAL == 1 */

#if (BLE_CFG_CENTRAL == 1)
  role |= GAP_CENTRAL_ROLE;
#endif /* BLE_CFG_CENTRAL == 1 */

/* USER CODE BEGIN Role_Mngt*/
// write our own random address to the bt stack
  ret = aci_hal_write_config_data(CONFIG_DATA_PUBADDR_OFFSET, CONFIG_DATA_PUBADDR_LEN, (uint8_t*) custom_p_bd_addr);
  if (ret != BLE_STATUS_SUCCESS)
  {
    APP_DBG_MSG("  Fail   : aci_hal_write_config_data command - CONFIG_DATA_PUBADDR_OFFSET, result: 0x%x \n", ret);
  }
  else
  {
    APP_DBG_MSG("  Success: aci_hal_write_config_data command - CONFIG_DATA_PUBADDR_OFFSET\n");
    APP_DBG_MSG("  Public Bluetooth Address: %02x:%02x:%02x:%02x:%02x:%02x\n",custom_p_bd_addr[5],custom_p_bd_addr[4],custom_p_bd_addr[3],custom_p_bd_addr[2],custom_p_bd_addr[1],custom_p_bd_addr[0]);
  }


/* USER CODE END Role_Mngt */

  if (role > 0)
  {
    const char *name = CFG_GAP_DEVICE_NAME;
    ret = aci_gap_init(role,
                       CFG_PRIVACY,
                       CFG_GAP_DEVICE_NAME_LENGTH,
                       &gap_service_handle,
                       &gap_dev_name_char_handle,
                       &gap_appearance_char_handle);

    if (ret != BLE_STATUS_SUCCESS)
    {
      APP_DBG_MSG("  Fail   : aci_gap_init command, result: 0x%x \n", ret);
    }
    else
    {
      APP_DBG_MSG("  Success: aci_gap_init command\n");
    }

    ret = aci_gatt_update_char_value(gap_service_handle, gap_dev_name_char_handle, 0, strlen(name), (uint8_t *) name);
    if (ret != BLE_STATUS_SUCCESS)
    {
      BLE_DBG_SVCCTL_MSG("  Fail   : aci_gatt_update_char_value - Device Name\n");
    }
    else
    {
      BLE_DBG_SVCCTL_MSG("  Success: aci_gatt_update_char_value - Device Name\n");
    }
  }

  ret = aci_gatt_update_char_value(gap_service_handle,
                                   gap_appearance_char_handle,
                                   0,
                                   2,
                                   (uint8_t *)&a_appearance);
  if (ret != BLE_STATUS_SUCCESS)
  {
    BLE_DBG_SVCCTL_MSG("  Fail   : aci_gatt_update_char_value - Appearance\n");
  }
  else
  {
    BLE_DBG_SVCCTL_MSG("  Success: aci_gatt_update_char_value - Appearance\n");
  }

  /**
   * Initialize Default PHY
   */
  ret = hci_le_set_default_phy(ALL_PHYS_PREFERENCE,TX_2M_PREFERRED,RX_2M_PREFERRED);
  if (ret != BLE_STATUS_SUCCESS)
  {
    APP_DBG_MSG("  Fail   : hci_le_set_default_phy command, result: 0x%x \n", ret);
  }
  else
  {
    APP_DBG_MSG("  Success: hci_le_set_default_phy command\n");
  }

  /**
   * Initialize IO capability
   */
  BleApplicationContext.BleApplicationContext_legacy.bleSecurityParam.ioCapability = CFG_IO_CAPABILITY;
  ret = aci_gap_set_io_capability(BleApplicationContext.BleApplicationContext_legacy.bleSecurityParam.ioCapability);
  if (ret != BLE_STATUS_SUCCESS)
  {
    APP_DBG_MSG("  Fail   : aci_gap_set_io_capability command, result: 0x%x \n", ret);
  }
  else
  {
    APP_DBG_MSG("  Success: aci_gap_set_io_capability command\n");
  }

  /**
   * Initialize authentication
   */
  BleApplicationContext.BleApplicationContext_legacy.bleSecurityParam.mitm_mode = CFG_MITM_PROTECTION;
  BleApplicationContext.BleApplicationContext_legacy.bleSecurityParam.encryptionKeySizeMin = CFG_ENCRYPTION_KEY_SIZE_MIN;
  BleApplicationContext.BleApplicationContext_legacy.bleSecurityParam.encryptionKeySizeMax = CFG_ENCRYPTION_KEY_SIZE_MAX;
  BleApplicationContext.BleApplicationContext_legacy.bleSecurityParam.Use_Fixed_Pin = CFG_USED_FIXED_PIN;
  BleApplicationContext.BleApplicationContext_legacy.bleSecurityParam.Fixed_Pin = CFG_FIXED_PIN;
  BleApplicationContext.BleApplicationContext_legacy.bleSecurityParam.bonding_mode = CFG_BONDING_MODE;
  /* USER CODE BEGIN Ble_Hci_Gap_Gatt_Init_1*/

  /* USER CODE END Ble_Hci_Gap_Gatt_Init_1*/

  ret = aci_gap_set_authentication_requirement(BleApplicationContext.BleApplicationContext_legacy.bleSecurityParam.bonding_mode,
                                               BleApplicationContext.BleApplicationContext_legacy.bleSecurityParam.mitm_mode,
                                               CFG_SC_SUPPORT,
                                               CFG_KEYPRESS_NOTIFICATION_SUPPORT,
                                               BleApplicationContext.BleApplicationContext_legacy.bleSecurityParam.encryptionKeySizeMin,
                                               BleApplicationContext.BleApplicationContext_legacy.bleSecurityParam.encryptionKeySizeMax,
                                               BleApplicationContext.BleApplicationContext_legacy.bleSecurityParam.Use_Fixed_Pin,
                                               BleApplicationContext.BleApplicationContext_legacy.bleSecurityParam.Fixed_Pin,
                                               CFG_IDENTITY_ADDRESS);
  if (ret != BLE_STATUS_SUCCESS)
  {
    APP_DBG_MSG("  Fail   : aci_gap_set_authentication_requirement command, result: 0x%x \n", ret);
  }
  else
  {
    APP_DBG_MSG("  Success: aci_gap_set_authentication_requirement command\n");
  }

  /**
   * Initialize whitelist
   */
  if (BleApplicationContext.BleApplicationContext_legacy.bleSecurityParam.bonding_mode)
  {
    ret = aci_gap_configure_whitelist();
    if (ret != BLE_STATUS_SUCCESS)
    {
      APP_DBG_MSG("  Fail   : aci_gap_configure_whitelist command, result: 0x%x \n", ret);
    }
    else
    {
      APP_DBG_MSG("  Success: aci_gap_configure_whitelist command\n");
    }
  }
  APP_DBG_MSG("==>> End Ble_Hci_Gap_Gatt_Init function\n\r");
}

static void Adv_Request(APP_BLE_ConnStatus_t NewStatus)
{
  tBleStatus ret = BLE_STATUS_INVALID_PARAMS;

  BleApplicationContext.Device_Connection_Status = NewStatus;
  /* Start Fast or Low Power Advertising */
  ret = aci_gap_set_discoverable(ADV_TYPE,
                                 CFG_FAST_CONN_ADV_INTERVAL_MIN,
                                 CFG_FAST_CONN_ADV_INTERVAL_MAX,
                                 CFG_BLE_ADDRESS_TYPE,
                                 ADV_FILTER,
                                 0,
                                 0,
                                 0,
                                 0,
                                 0,
                                 0);
  if (ret != BLE_STATUS_SUCCESS)
  {
    APP_DBG_MSG("==>> aci_gap_set_discoverable - fail, result: 0x%x \n", ret);
  }
  else
  {
    APP_DBG_MSG("==>> aci_gap_set_discoverable - Success\n");
  }

/* USER CODE BEGIN Adv_Request_1*/
  // send a custom advertisement packet

  /* Remove the TX power level advertisement (this is done to decrease the packet size). */

  ret = aci_gap_delete_ad_type(AD_TYPE_TX_POWER_LEVEL);
  ret |= aci_gap_delete_ad_type(AD_TYPE_FLAGS);

  if (ret != BLE_STATUS_SUCCESS)
  {
    return;
  }

  /* Update Advertising data */
  ret = aci_gap_update_adv_data(sizeof(custom_a_AdvData), (uint8_t*) custom_a_AdvData);
  if (ret != BLE_STATUS_SUCCESS)
  {
      APP_DBG_MSG("==>> Start Fast Advertising Failed , result: %d \n\r", ret);
  }
  else
  {
      APP_DBG_MSG("==>> Success: Start Fast Advertising \n\r");
  }

  return; // skip the cube generated a_AdvData sending
/* USER CODE END Adv_Request_1*/

  /* Update Advertising data */
  ret = aci_gap_update_adv_data(sizeof(a_AdvData), (uint8_t*) a_AdvData);
  if (ret != BLE_STATUS_SUCCESS)
  {
      APP_DBG_MSG("==>> Start Fast Advertising Failed , result: %d \n\r", ret);
  }
  else
  {
      APP_DBG_MSG("==>> Success: Start Fast Advertising \n\r");
  }

  return;
}

const uint8_t* BleGetBdAddress(void)
{
  uint8_t *p_otp_addr;
  const uint8_t *p_bd_addr;
  uint32_t udn;
  uint32_t company_id;
  uint32_t device_id;

  udn = LL_FLASH_GetUDN();

  if (udn != 0xFFFFFFFF)
  {
    company_id = LL_FLASH_GetSTCompanyID();
    device_id = LL_FLASH_GetDeviceID();

    /**
     * Public Address with the ST company ID
     * bit[47:24] : 24bits (OUI) equal to the company ID
     * bit[23:16] : Device ID.
     * bit[15:0] : The last 16bits from the UDN
     * Note: In order to use the Public Address in a final product, a dedicated
     * 24bits company ID (OUI) shall be bought.
     */
    a_BdAddrUdn[0] = (uint8_t)(udn & 0x000000FF);
    a_BdAddrUdn[1] = (uint8_t)((udn & 0x0000FF00) >> 8);
    a_BdAddrUdn[2] = (uint8_t)device_id;
    a_BdAddrUdn[3] = (uint8_t)(company_id & 0x000000FF);
    a_BdAddrUdn[4] = (uint8_t)((company_id & 0x0000FF00) >> 8);
    a_BdAddrUdn[5] = (uint8_t)((company_id & 0x00FF0000) >> 16);

    p_bd_addr = (const uint8_t *)a_BdAddrUdn;
  }
  else
  {
    p_otp_addr = OTP_Read(0);
    if (p_otp_addr)
    {
      p_bd_addr = ((OTP_ID0_t*)p_otp_addr)->bd_address;
    }
    else
    {
      p_bd_addr = a_MBdAddr;
    }
  }

  return p_bd_addr;
}

/*************************************************************
 *
 * SPECIFIC FUNCTIONS FOR CUSTOM
 *
 *************************************************************/
static void Adv_Cancel(void)
{
  if (BleApplicationContext.Device_Connection_Status != APP_BLE_CONNECTED_SERVER)
  {
    tBleStatus ret = BLE_STATUS_INVALID_PARAMS;

    ret = aci_gap_set_non_discoverable();

    BleApplicationContext.Device_Connection_Status = APP_BLE_IDLE;
    if (ret != BLE_STATUS_SUCCESS)
    {
      APP_DBG_MSG("** STOP ADVERTISING **  Failed \r\n\r");
    }
    else
    {
      APP_DBG_MSG("  \r\n\r");
      APP_DBG_MSG("** STOP ADVERTISING **  \r\n\r");
    }
  }

  return;
}

#if (L2CAP_REQUEST_NEW_CONN_PARAM != 0)
void BLE_SVC_L2CAP_Conn_Update(uint16_t ConnectionHandle)
{
  if (mutex == 1)
  {
    mutex = 0;
    index_con_int = (index_con_int + 1)%SIZE_TAB_CONN_INT;
    uint16_t interval_min = CONN_P(a_ConnInterval[index_con_int]);
    uint16_t interval_max = CONN_P(a_ConnInterval[index_con_int]);
    uint16_t peripheral_latency = L2CAP_PERIPHERAL_LATENCY;
    uint16_t timeout_multiplier = L2CAP_TIMEOUT_MULTIPLIER;
    tBleStatus ret;

    ret = aci_l2cap_connection_parameter_update_req(BleApplicationContext.BleApplicationContext_legacy.connectionHandle,
                                                    interval_min, interval_max,
                                                    peripheral_latency, timeout_multiplier);
    if (ret != BLE_STATUS_SUCCESS)
    {
      APP_DBG_MSG("BLE_SVC_L2CAP_Conn_Update(), Failed \r\n\r");
    }
    else
    {
      APP_DBG_MSG("BLE_SVC_L2CAP_Conn_Update(), Successfully \r\n\r");
    }
  }

  return;
}
#endif /* L2CAP_REQUEST_NEW_CONN_PARAM != 0 */

#if (L2CAP_REQUEST_NEW_CONN_PARAM != 0)
static void Connection_Interval_Update_Req(void)
{
  if (BleApplicationContext.Device_Connection_Status != APP_BLE_FAST_ADV && BleApplicationContext.Device_Connection_Status != APP_BLE_IDLE)
  {
    BLE_SVC_L2CAP_Conn_Update(BleApplicationContext.BleApplicationContext_legacy.connectionHandle);
  }

  return;
}
#endif /* L2CAP_REQUEST_NEW_CONN_PARAM != 0 */

/*************************************************************
 *
 * WRAP FUNCTIONS
 *
 *************************************************************/
void hci_notify_asynch_evt(void* p_Data)
{
  UTIL_SEQ_SetTask(1 << CFG_TASK_HCI_ASYNCH_EVT_ID, CFG_SCH_PRIO_0);

  return;
}

void hci_cmd_resp_release(uint32_t Flag)
{
  UTIL_SEQ_SetEvt(1 << CFG_IDLEEVT_HCI_CMD_EVT_RSP_ID);

  return;
}

void hci_cmd_resp_wait(uint32_t Timeout)
{
  UTIL_SEQ_WaitEvt(1 << CFG_IDLEEVT_HCI_CMD_EVT_RSP_ID);

  return;
}

static void BLE_UserEvtRx(void *p_Payload)
{
  SVCCTL_UserEvtFlowStatus_t svctl_return_status;
  tHCI_UserEvtRxParam *p_param;

  p_param = (tHCI_UserEvtRxParam *)p_Payload;

  svctl_return_status = SVCCTL_UserEvtRx((void *)&(p_param->pckt->evtserial));
  if (svctl_return_status != SVCCTL_UserEvtFlowDisable)
  {
    p_param->status = HCI_TL_UserEventFlow_Enable;
  }
  else
  {
    p_param->status = HCI_TL_UserEventFlow_Disable;
  }

  return;
}

static void BLE_StatusNot(HCI_TL_CmdStatus_t Status)
{
  uint32_t task_id_list;
  switch (Status)
  {
    case HCI_TL_CmdBusy:
      /**
       * All tasks that may send an aci/hci commands shall be listed here
       * This is to prevent a new command is sent while one is already pending
       */
      task_id_list = (1 << CFG_LAST_TASK_ID_WITH_HCICMD) - 1;
      UTIL_SEQ_PauseTask(task_id_list);
      break;

    case HCI_TL_CmdAvailable:
      /**
       * All tasks that may send an aci/hci commands shall be listed here
       * This is to prevent a new command is sent while one is already pending
       */
      task_id_list = (1 << CFG_LAST_TASK_ID_WITH_HCICMD) - 1;
      UTIL_SEQ_ResumeTask(task_id_list);
      break;

    default:
      break;
  }

  return;
}

void SVCCTL_ResumeUserEventFlow(void)
{
  hci_resume_flow();

  return;
}
